AN00927/E-inkAware/Design Progress Photos/Screenshot 2025-12-28 152636.png

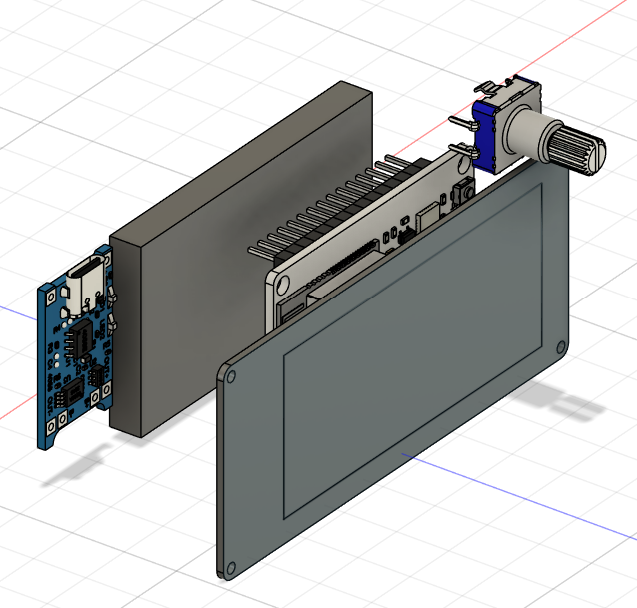
Design Progress Photos/Screenshot 2025-12-28 152636.png
