AN00927/E-inkAware/E-ink 3D Render.png

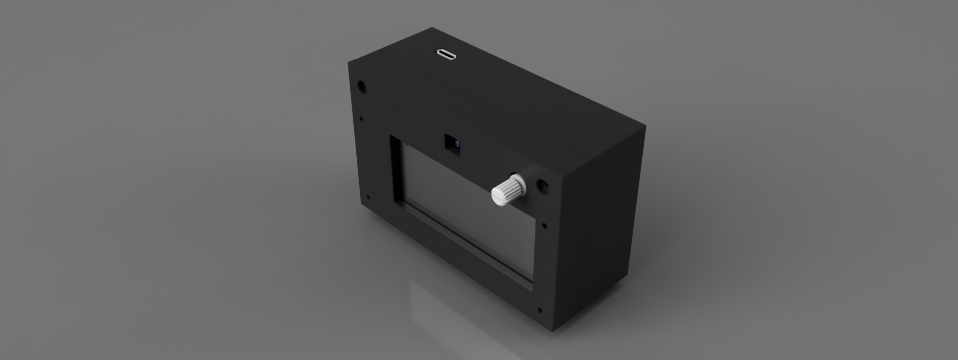
E-ink 3D Render.png
