AN00927/E-inkAware/Physical Progress Photos/MOSFETSize.jpeg

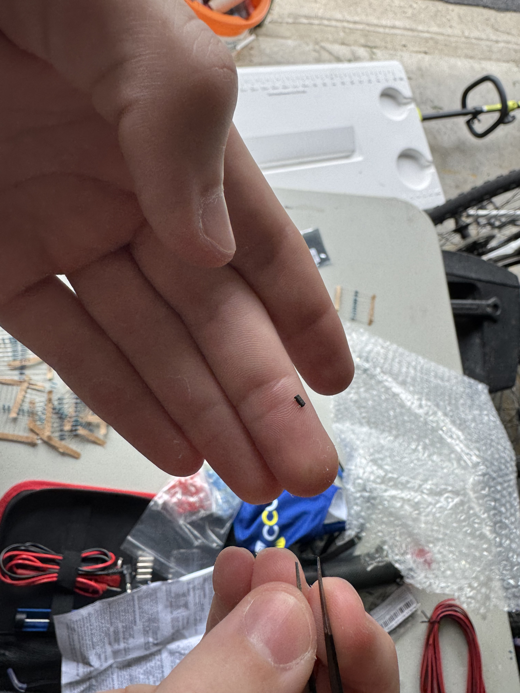
Physical Progress Photos/MOSFETSize.jpeg
