AN00927/E-inkAware/Physical Progress Photos/MOSFETSoldered.jpeg

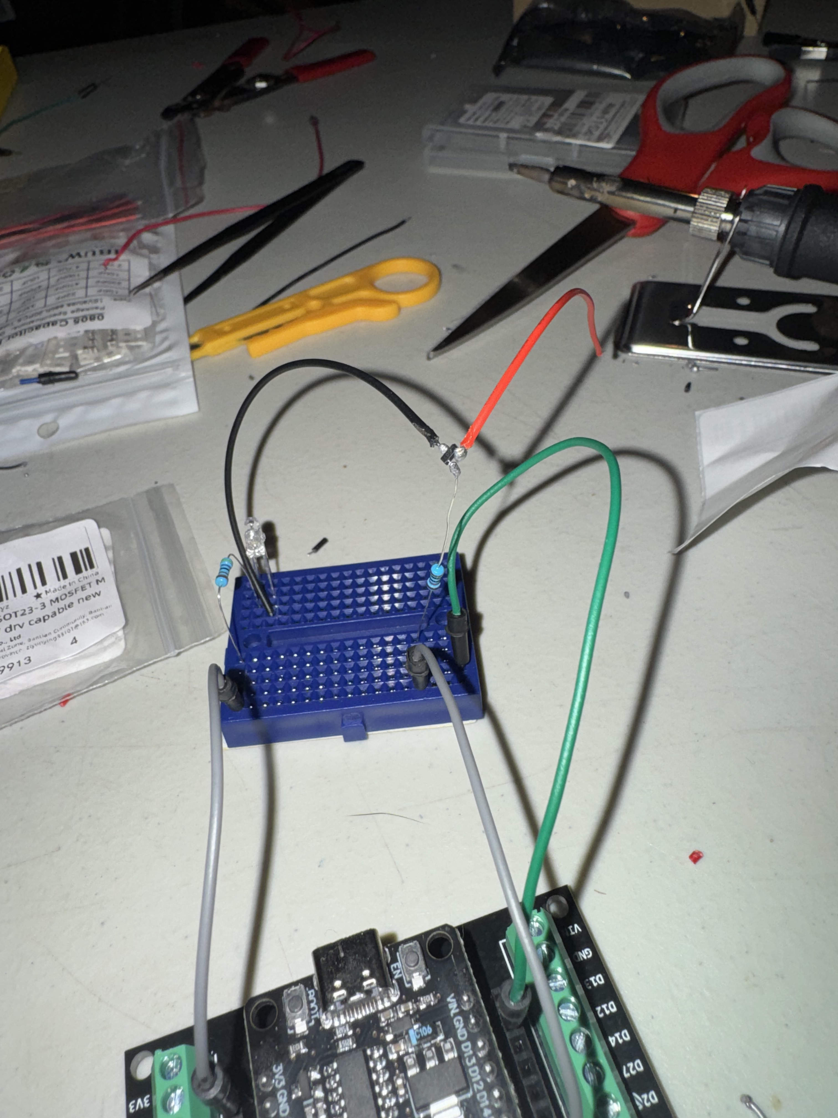
Physical Progress Photos/MOSFETSoldered.jpeg
