AN00927/E-inkAware/Physical Progress Photos/TestingESP32.jpeg

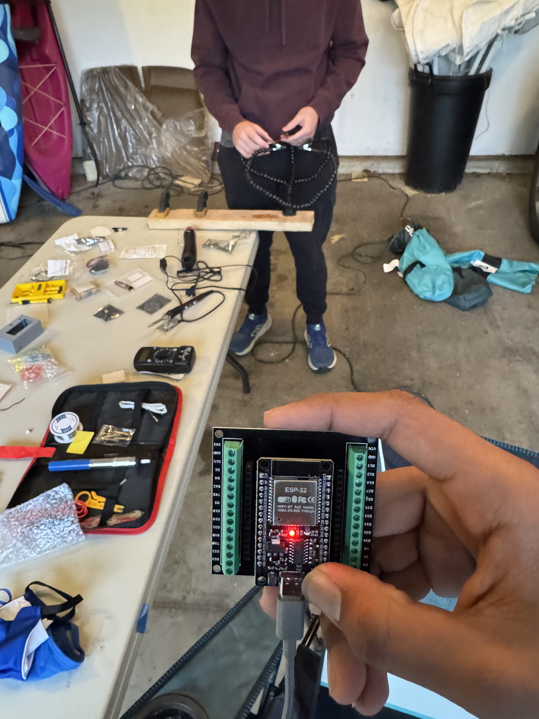
Physical Progress Photos/TestingESP32.jpeg
