AN00927/E-inkAware/Schematic Files/light-aware-eink.kicad_sch

## KiCad design Schematic Files/light-aware-eink.kicad_sch (2026-03-11)

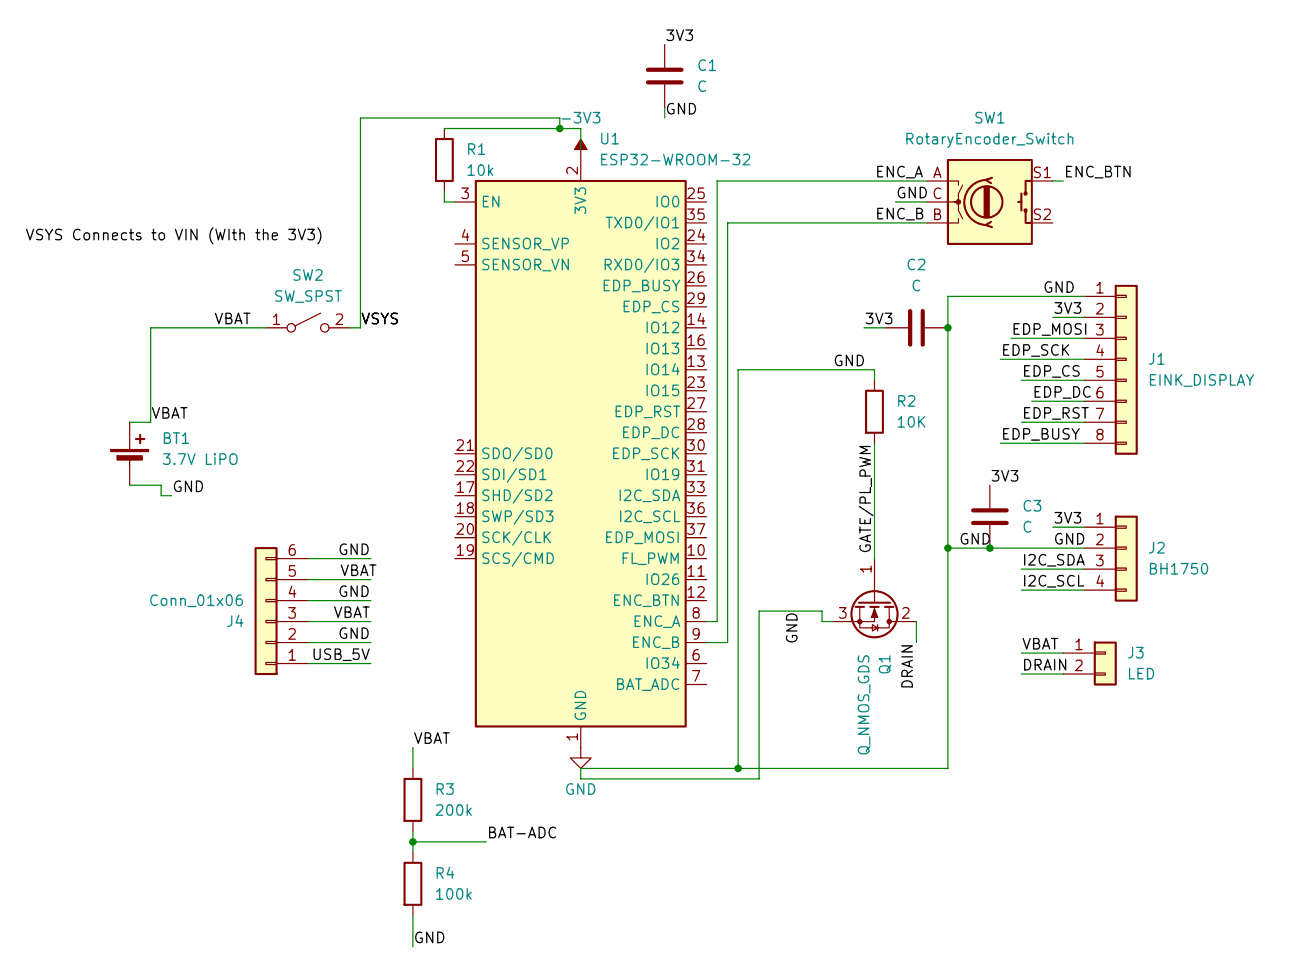
[picture p19: schematic light-aware-eink.kicad_sch]

Parts:
BT1: 3.7V LiPO
C1, C2, C3: C
J1: EINK_DISPLAY
J2: BH1750
J3: LED
J4: Conn_01x06
Q1: Q_NMOS_GDS
R1: 10k
R2: 10K
R3: 200k
R4: 100k
SW1: RotaryEncoder_Switch
SW2: SW_SPST
U1: ESP32-WROOM-32

Connections:
3V3: C1.1, C2.1, C3.1, J1.2, J2.1
-3V3: U1.2 (3V3)
BAT-ADC: R3.2, R4.1
DRAIN: J3.2, Q1.2 (D)
EDP_BUSY: J1.8
EDP_CS: J1.5
EDP_DC: J1.6
EDP_MOSI: J1.3
EDP_RST: J1.7
EDP_SCK: J1.4
ENC_A: SW1.A, U1.8 (ENC_A)
ENC_B: SW1.B, U1.9 (ENC_B)
ENC_BTN: SW1.S1
GATE/PL_PWM: Q1.1 (G), R2.2
GND: BT1.2 (-), C1.2, C2.2, C3.2, J1.1, J2.2, J4.2, J4.4, J4.6, Q1.3 (S), R2.1, R4.2, SW1.C, U1.1 (GND), U1.15 (GND), U1.38 (GND), U1.39 (GND)
I2C_SCL: J2.4
I2C_SDA: J2.3
unnamed: R1.2, U1.3 (EN)
USB_5V: J4.1
VBAT: BT1.1 (+), J3.1, J4.3, J4.5, R3.1, SW2.1 (A)
VSYS: R1.1, SW2.2 (B)
