AN00927/E-inkAware/Physical Progress Photos/SecondDay.jpeg

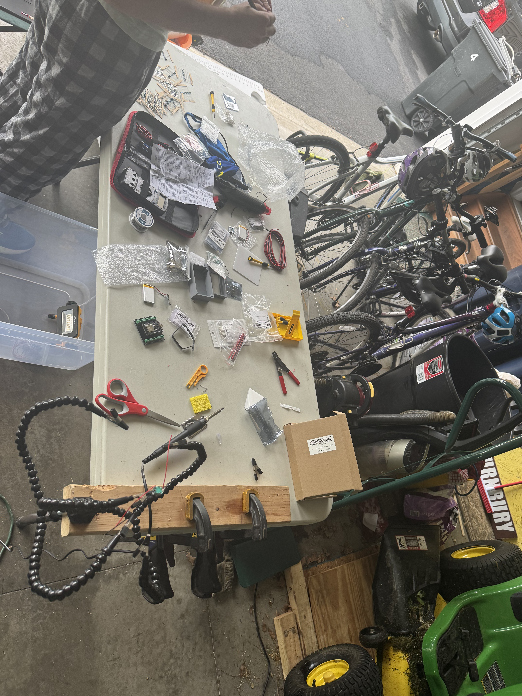
Physical Progress Photos/SecondDay.jpeg
