AN00927/E-inkAware/Physical Progress Photos/LEDCircuitTest.jpeg

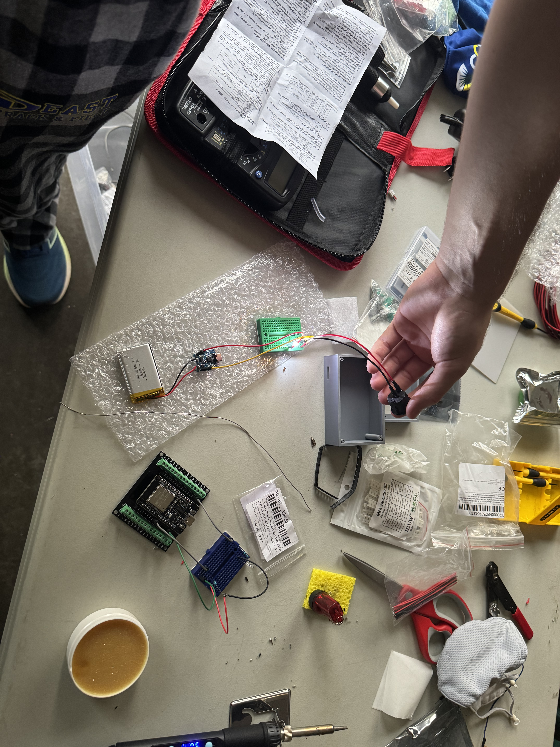
Physical Progress Photos/LEDCircuitTest.jpeg
